Gekkio/gb-research/mbc1b/schematic/MBC1B.kicad_sch

## KiCad design mbc1b/schematic/MBC1B.kicad_sch (2024-04-07)

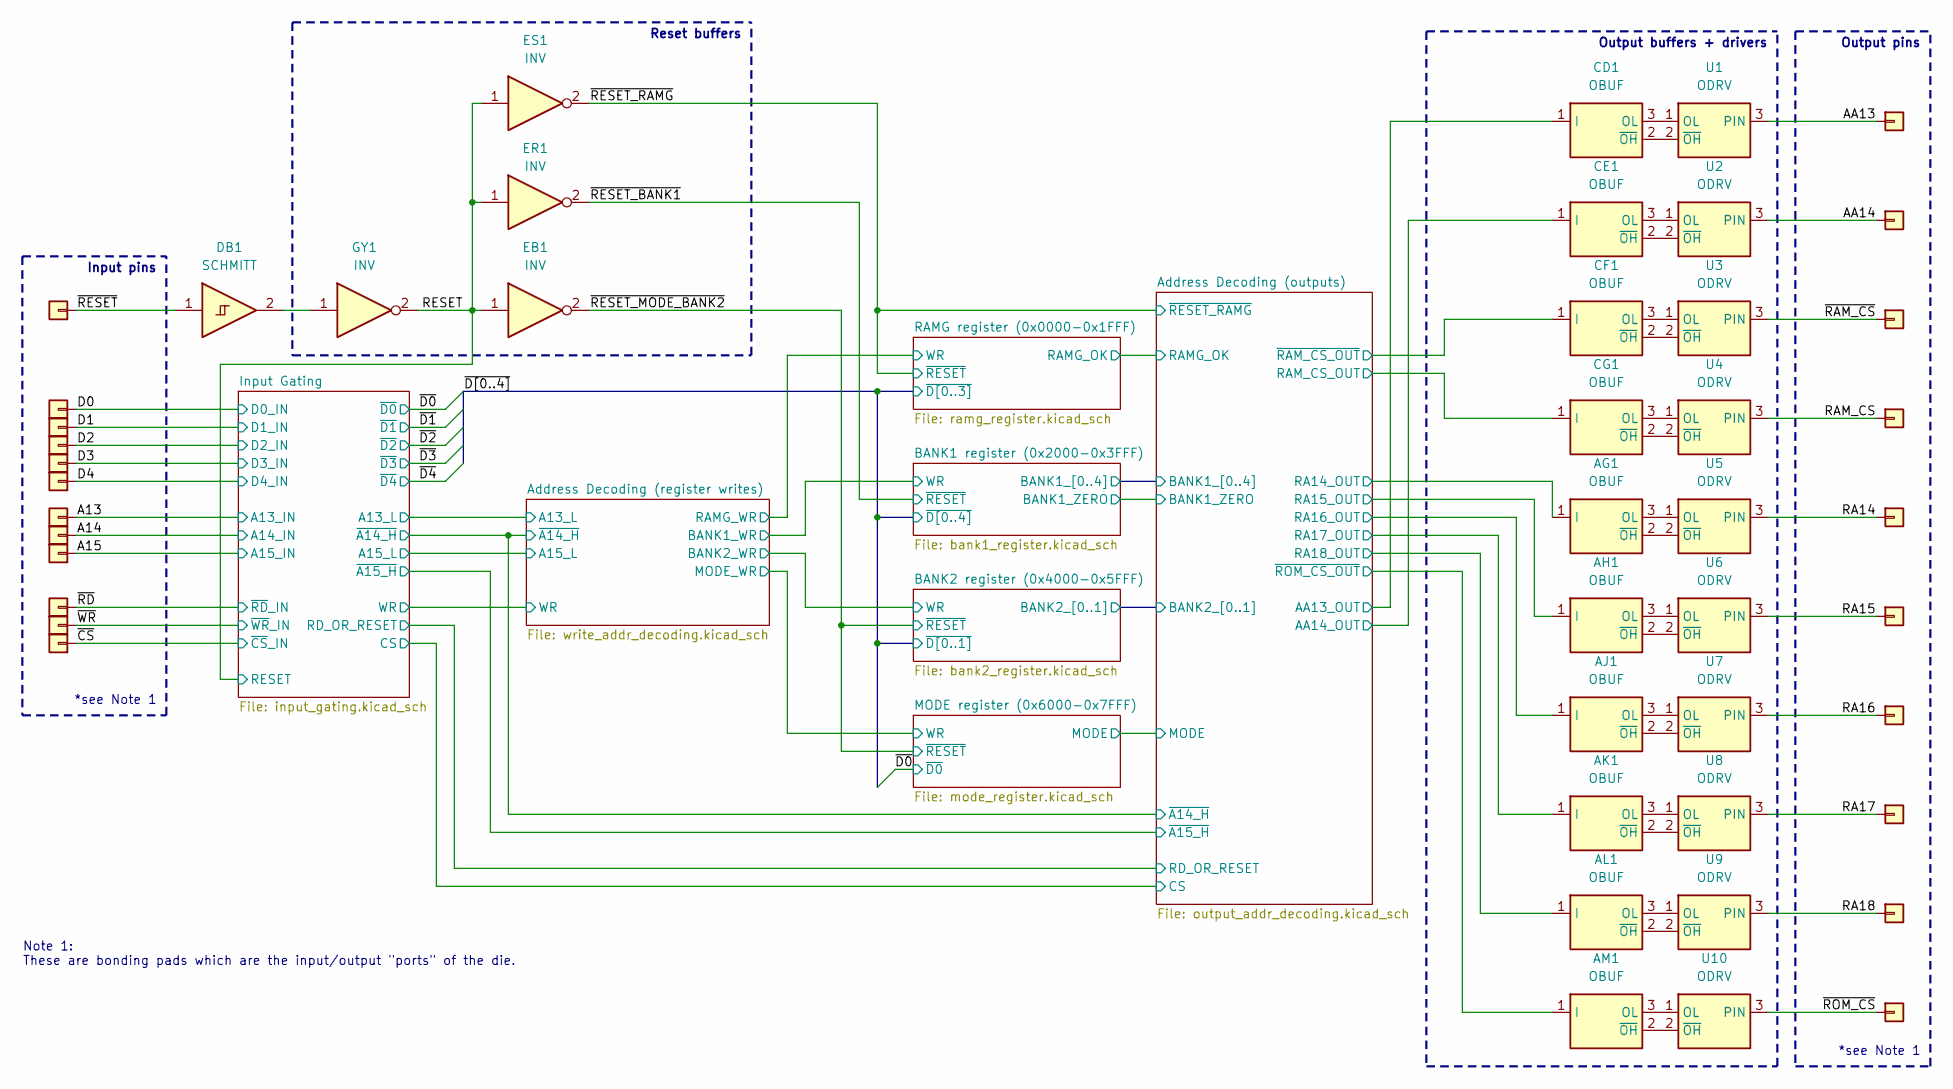
[picture p10: schematic MBC1B.kicad_sch]

Parts:
A1, A2, A3, A4, A5, A6, A7, A8, A9, A10, A11, A12, A13, A14, A15, A16, A17, A18, A19, A20, A21, A22: (no value)
AG1: OBUF
AH1: OBUF
AJ1: OBUF
AK1: OBUF
AL1: OBUF
AM1: OBUF
CD1: OBUF
CE1: OBUF
CF1: OBUF
CG1: OBUF
DB1: SCHMITT
EB1: INV
ER1: INV
ES1: INV
GY1: INV
U1, U2, U3, U4, U5, U6, U7, U8, U9, U10: ODRV

Connections:
A13: A7.1
A14: A8.1
A15: A9.1
AA13: A13.1, U1.3 (PIN)
AA13_OUT: CD1.1 (I)
AA14: A14.1, U2.3 (PIN)
AA14_OUT: CE1.1 (I)
D0: A2.1
D1: A3.1
D2: A4.1
D3: A5.1
D4: A6.1
unnamed: AG1.2 (~OH), U5.2 (~OH)
unnamed: AG1.3 (OL), U5.1 (OL)
unnamed: AH1.2 (~OH), U6.2 (~OH)
unnamed: AH1.3 (OL), U6.1 (OL)
unnamed: AJ1.2 (~OH), U7.2 (~OH)
unnamed: AJ1.3 (OL), U7.1 (OL)
unnamed: AK1.2 (~OH), U8.2 (~OH)
unnamed: AK1.3 (OL), U8.1 (OL)
unnamed: AL1.2 (~OH), U9.2 (~OH)
unnamed: AL1.3 (OL), U9.1 (OL)
unnamed: AM1.2 (~OH), U10.2 (~OH)
unnamed: AM1.3 (OL), U10.1 (OL)
unnamed: CD1.2 (~OH), U1.2 (~OH)
unnamed: CD1.3 (OL), U1.1 (OL)
unnamed: CE1.2 (~OH), U2.2 (~OH)
unnamed: CE1.3 (OL), U2.1 (OL)
unnamed: CF1.2 (~OH), U3.2 (~OH)
unnamed: CF1.3 (OL), U3.1 (OL)
unnamed: CG1.2 (~OH), U4.2 (~OH)
unnamed: CG1.3 (OL), U4.1 (OL)
unnamed: DB1.2 (Y), GY1.1 (A)
RA14: A17.1, U5.3 (PIN)
RA14_OUT: AG1.1 (I)
RA15: A18.1, U6.3 (PIN)
RA15_OUT: AH1.1 (I)
RA16: A19.1, U7.3 (PIN)
RA16_OUT: AJ1.1 (I)
RA17: A20.1, U8.3 (PIN)
RA17_OUT: AK1.1 (I)
RA18: A21.1, U9.3 (PIN)
RA18_OUT: AL1.1 (I)
RAM_CS: A16.1, U4.3 (PIN)
RAM_CS_OUT: CG1.1 (I)
RESET: EB1.1 (A), ER1.1 (A), ES1.1 (A), GY1.2 (Y)
~CS: A12.1
~RAM_CS_OUT: CF1.1 (I)
~RAM_CS: A15.1, U3.3 (PIN)
~RD: A10.1
~RESET_BANK1: ER1.2 (Y)
~RESET_MODE_BANK2: EB1.2 (Y)
~RESET_RAMG: ES1.2 (Y)
~RESET: A1.1, DB1.1 (A)
~ROM_CS_OUT: AM1.1 (I)
~ROM_CS: A22.1, U10.3 (PIN)
~WR: A11.1

Notes on the sheet:
Note 1: These are bonding pads which are the input/output "ports" of the die.
Input pins
*see Note 1
Output buffers + drivers
Output pins
Reset buffers
