Gekkio/gb-research/mbc1b/schematic/bank1_register.kicad_sch

## KiCad design mbc1b/schematic/bank1_register.kicad_sch (2024-04-07)

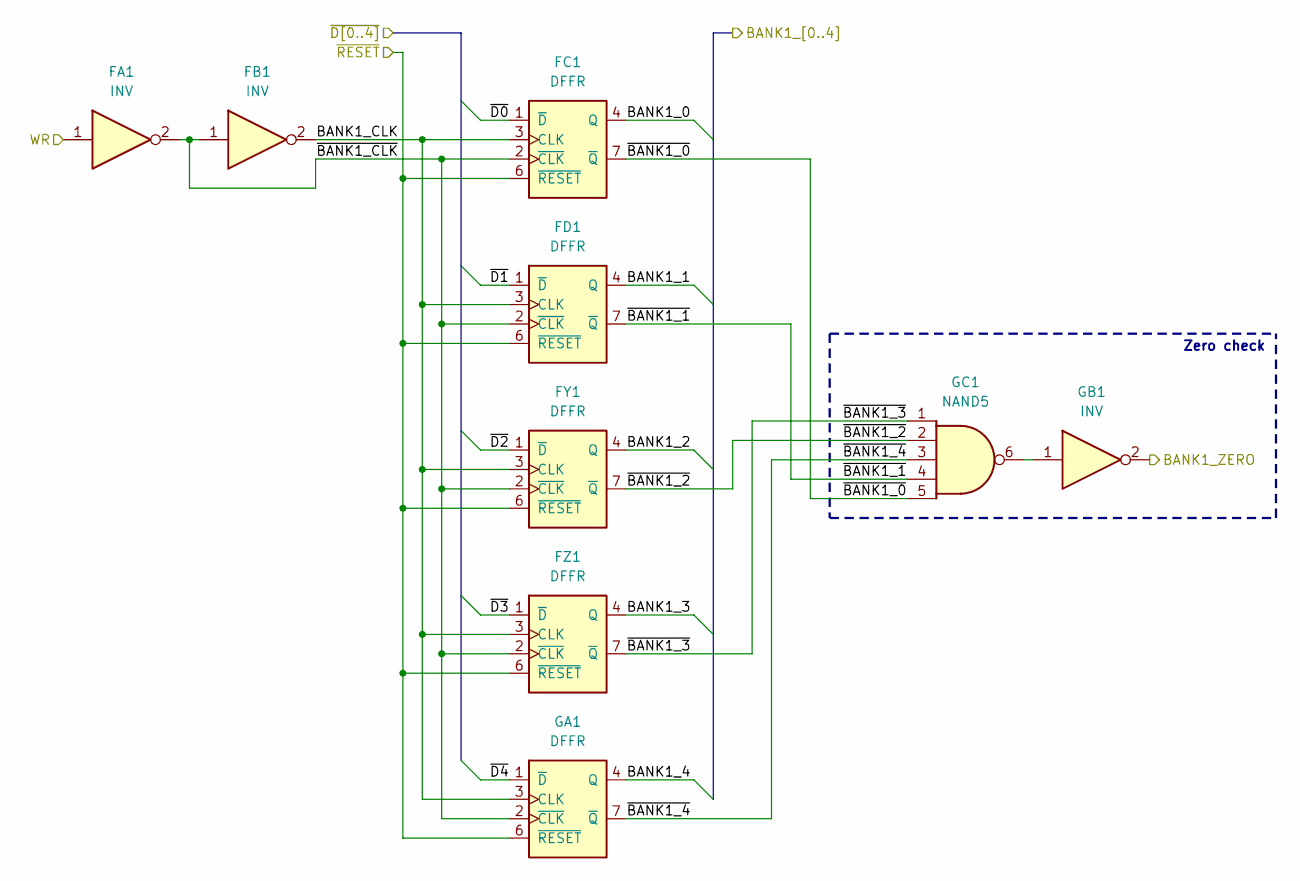
[picture p11: schematic bank1_register.kicad_sch]

Parts:
FA1: INV
FB1: INV
FC1: DFFR
FD1: DFFR
FY1: DFFR
FZ1: DFFR
GA1: DFFR
GB1: INV
GC1: NAND5

Connections:
BANK1_0: FC1.4 (Q)
BANK1_1: FD1.4 (Q)
BANK1_2: FY1.4 (Q)
BANK1_3: FZ1.4 (Q)
BANK1_4: GA1.4 (Q)
BANK1_CLK: FB1.2 (Y), FC1.3 (CLK), FD1.3 (CLK), FY1.3 (CLK), FZ1.3 (CLK), GA1.3 (CLK)
BANK1_ZERO: GB1.2 (Y)
unnamed: GB1.1 (A), GC1.6 (Y)
WR: FA1.1 (A)
~BANK1_0: FC1.7 (~Q), GC1.5 (E)
~BANK1_1: FD1.7 (~Q), GC1.4 (D)
~BANK1_2: FY1.7 (~Q), GC1.2 (B)
~BANK1_3: FZ1.7 (~Q), GC1.1 (A)
~BANK1_4: GA1.7 (~Q), GC1.3 (C)
~BANK1_CLK: FA1.2 (Y), FB1.1 (A), FC1.2 (~CLK), FD1.2 (~CLK), FY1.2 (~CLK), FZ1.2 (~CLK), GA1.2 (~CLK)
~D0: FC1.1 (~D)
~D1: FD1.1 (~D)
~D2: FY1.1 (~D)
~D3: FZ1.1 (~D)
~D4: GA1.1 (~D)
~RESET: FC1.6 (~RESET), FD1.6 (~RESET), FY1.6 (~RESET), FZ1.6 (~RESET), GA1.6 (~RESET)

Notes on the sheet:
Zero check
