Gekkio/gb-research/mbc1b/schematic/bank2_register.kicad_sch

## KiCad design mbc1b/schematic/bank2_register.kicad_sch (2024-04-07)

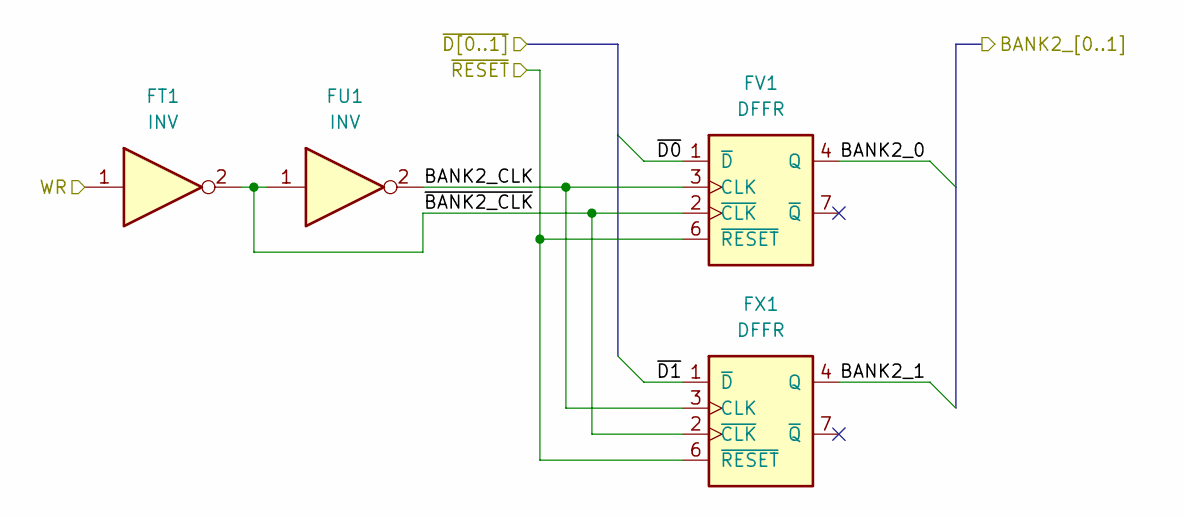
[picture p12: schematic bank2_register.kicad_sch]

Parts:
FT1: INV
FU1: INV
FV1: DFFR
FX1: DFFR

Connections:
BANK2_0: FV1.4 (Q)
BANK2_1: FX1.4 (Q)
BANK2_CLK: FU1.2 (Y), FV1.3 (CLK), FX1.3 (CLK)
WR: FT1.1 (A)
~BANK2_CLK: FT1.2 (Y), FU1.1 (A), FV1.2 (~CLK), FX1.2 (~CLK)
~D0: FV1.1 (~D)
~D1: FX1.1 (~D)
~RESET: FV1.6 (~RESET), FX1.6 (~RESET)
