Gekkio/gb-research/mbc1b/schematic/input_gates.kicad_sch

## KiCad design mbc1b/schematic/input_gates.kicad_sch (2022-03-13)

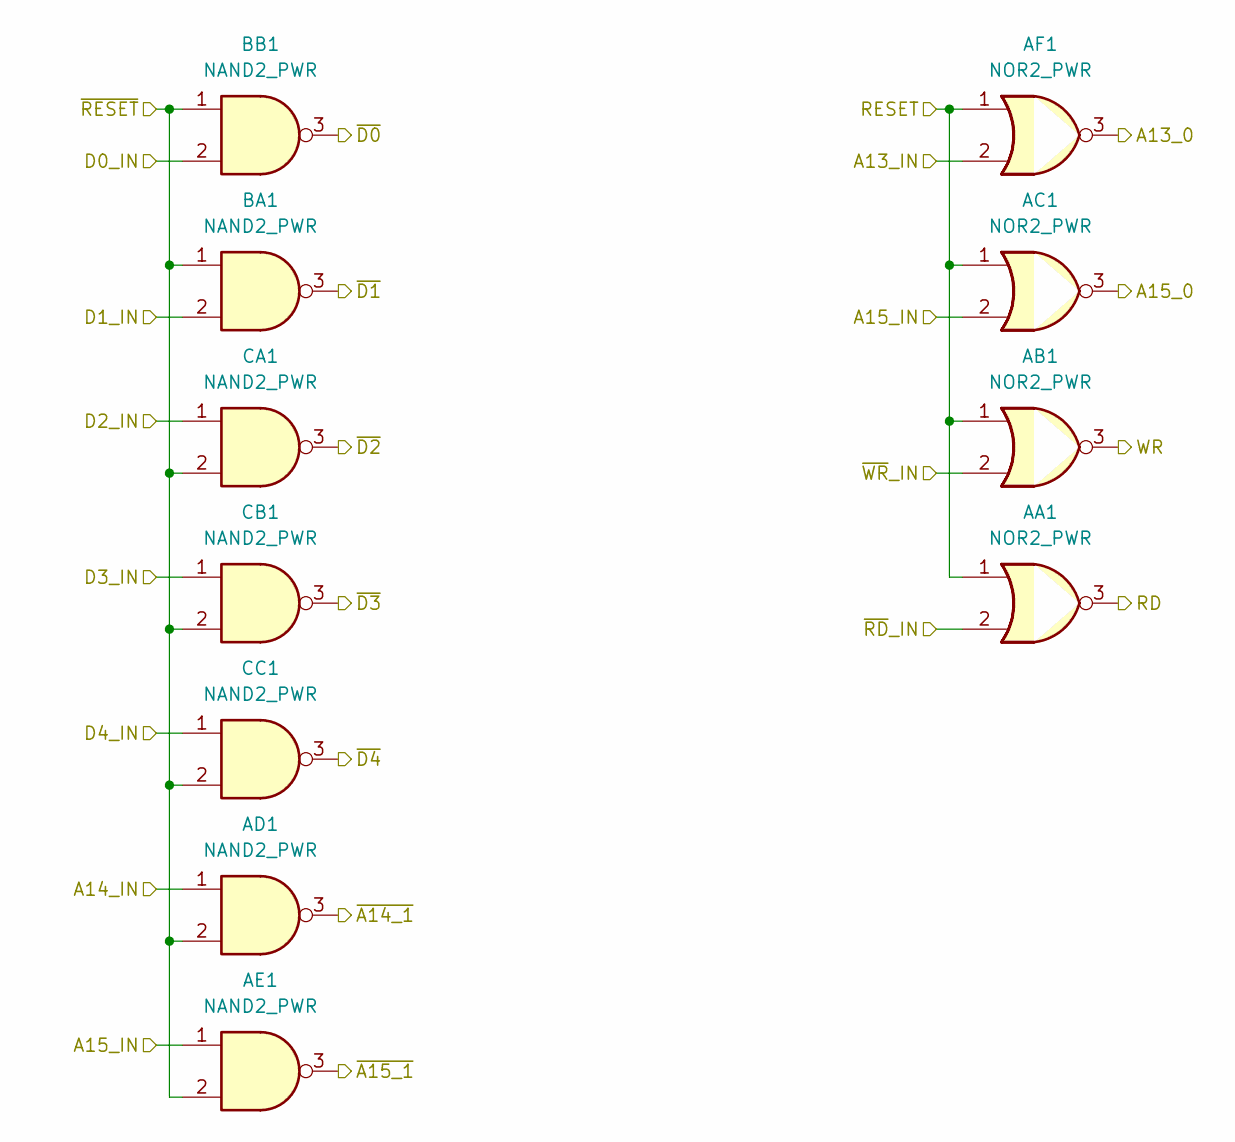
[picture p13: schematic input_gates.kicad_sch]

Parts:
AA1: NOR2_PWR
AB1: NOR2_PWR
AC1: NOR2_PWR
AD1: NAND2_PWR
AE1: NAND2_PWR
AF1: NOR2_PWR
BA1: NAND2_PWR
BB1: NAND2_PWR
CA1: NAND2_PWR
CB1: NAND2_PWR
CC1: NAND2_PWR

Connections:
A13_0: AF1.3 (Y)
A13_IN: AF1.2 (B)
A14_IN: AD1.1 (A)
A15_0: AC1.3 (Y)
A15_IN: AC1.2 (B), AE1.1 (A)
D0_IN: BB1.2 (B)
D1_IN: BA1.2 (B)
D2_IN: CA1.1 (A)
D3_IN: CB1.1 (A)
D4_IN: CC1.1 (A)
RD: AA1.3 (Y)
RESET: AA1.1 (A), AB1.1 (A), AC1.1 (A), AF1.1 (A)
WR: AB1.3 (Y)
~A14_1: AD1.3 (Y)
~A15_1: AE1.3 (Y)
~D0: BB1.3 (Y)
~D1: BA1.3 (Y)
~D2: CA1.3 (Y)
~D3: CB1.3 (Y)
~D4: CC1.3 (Y)
~RD_IN: AA1.2 (B)
~RESET: AD1.2 (B), AE1.2 (B), BA1.1 (A), BB1.1 (A), CA1.2 (B), CB1.2 (B), CC1.2 (B)
~WR_IN: AB1.2 (B)
