Gekkio/gb-research/mbc1b/schematic/input_gating.kicad_sch

## KiCad design mbc1b/schematic/input_gating.kicad_sch (2024-04-07)

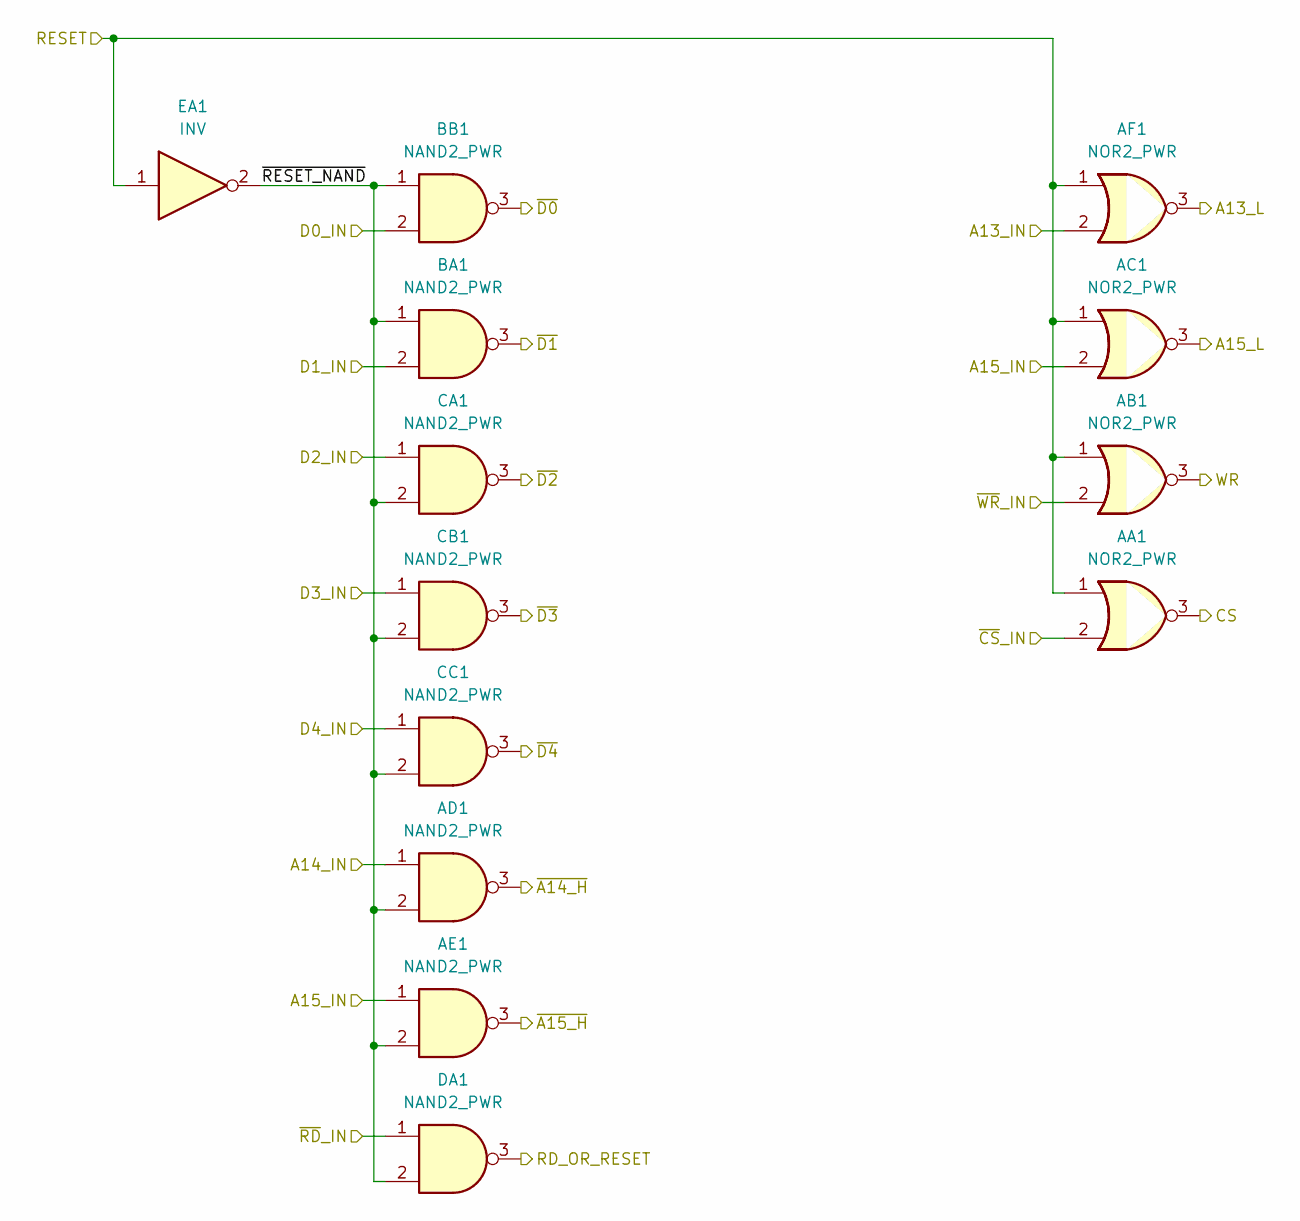
[picture p14: schematic input_gating.kicad_sch]

Parts:
AA1: NOR2_PWR
AB1: NOR2_PWR
AC1: NOR2_PWR
AD1: NAND2_PWR
AE1: NAND2_PWR
AF1: NOR2_PWR
BA1: NAND2_PWR
BB1: NAND2_PWR
CA1: NAND2_PWR
CB1: NAND2_PWR
CC1: NAND2_PWR
DA1: NAND2_PWR
EA1: INV

Connections:
A13_IN: AF1.2 (B)
A13_L: AF1.3 (Y)
A14_IN: AD1.1 (A)
A15_IN: AC1.2 (B), AE1.1 (A)
A15_L: AC1.3 (Y)
CS: AA1.3 (Y)
D0_IN: BB1.2 (B)
D1_IN: BA1.2 (B)
D2_IN: CA1.1 (A)
D3_IN: CB1.1 (A)
D4_IN: CC1.1 (A)
RD_OR_RESET: DA1.3 (Y)
RESET: AA1.1 (A), AB1.1 (A), AC1.1 (A), AF1.1 (A), EA1.1 (A)
WR: AB1.3 (Y)
~A14_H: AD1.3 (Y)
~A15_H: AE1.3 (Y)
~CS_IN: AA1.2 (B)
~D0: BB1.3 (Y)
~D1: BA1.3 (Y)
~D2: CA1.3 (Y)
~D3: CB1.3 (Y)
~D4: CC1.3 (Y)
~RD_IN: DA1.1 (A)
~RESET_NAND: AD1.2 (B), AE1.2 (B), BA1.1 (A), BB1.1 (A), CA1.2 (B), CB1.2 (B), CC1.2 (B), DA1.2 (B), EA1.2 (Y)
~WR_IN: AB1.2 (B)
