Gekkio/gb-research/mbc1b/schematic/mode_register.kicad_sch

## KiCad design mbc1b/schematic/mode_register.kicad_sch (2024-04-07)

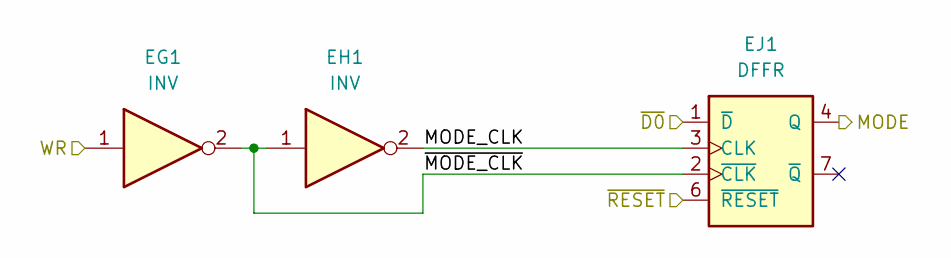
[picture p15: schematic mode_register.kicad_sch]

Parts:
EG1: INV
EH1: INV
EJ1: DFFR

Connections:
MODE: EJ1.4 (Q)
MODE_CLK: EH1.2 (Y), EJ1.3 (CLK)
WR: EG1.1 (A)
~D0: EJ1.1 (~D)
~MODE_CLK: EG1.2 (Y), EH1.1 (A), EJ1.2 (~CLK)
~RESET: EJ1.6 (~RESET)
