Gekkio/gb-research/mbc1b/schematic/output_addr_decoding.kicad_sch

## KiCad design mbc1b/schematic/output_addr_decoding.kicad_sch (2024-04-07)

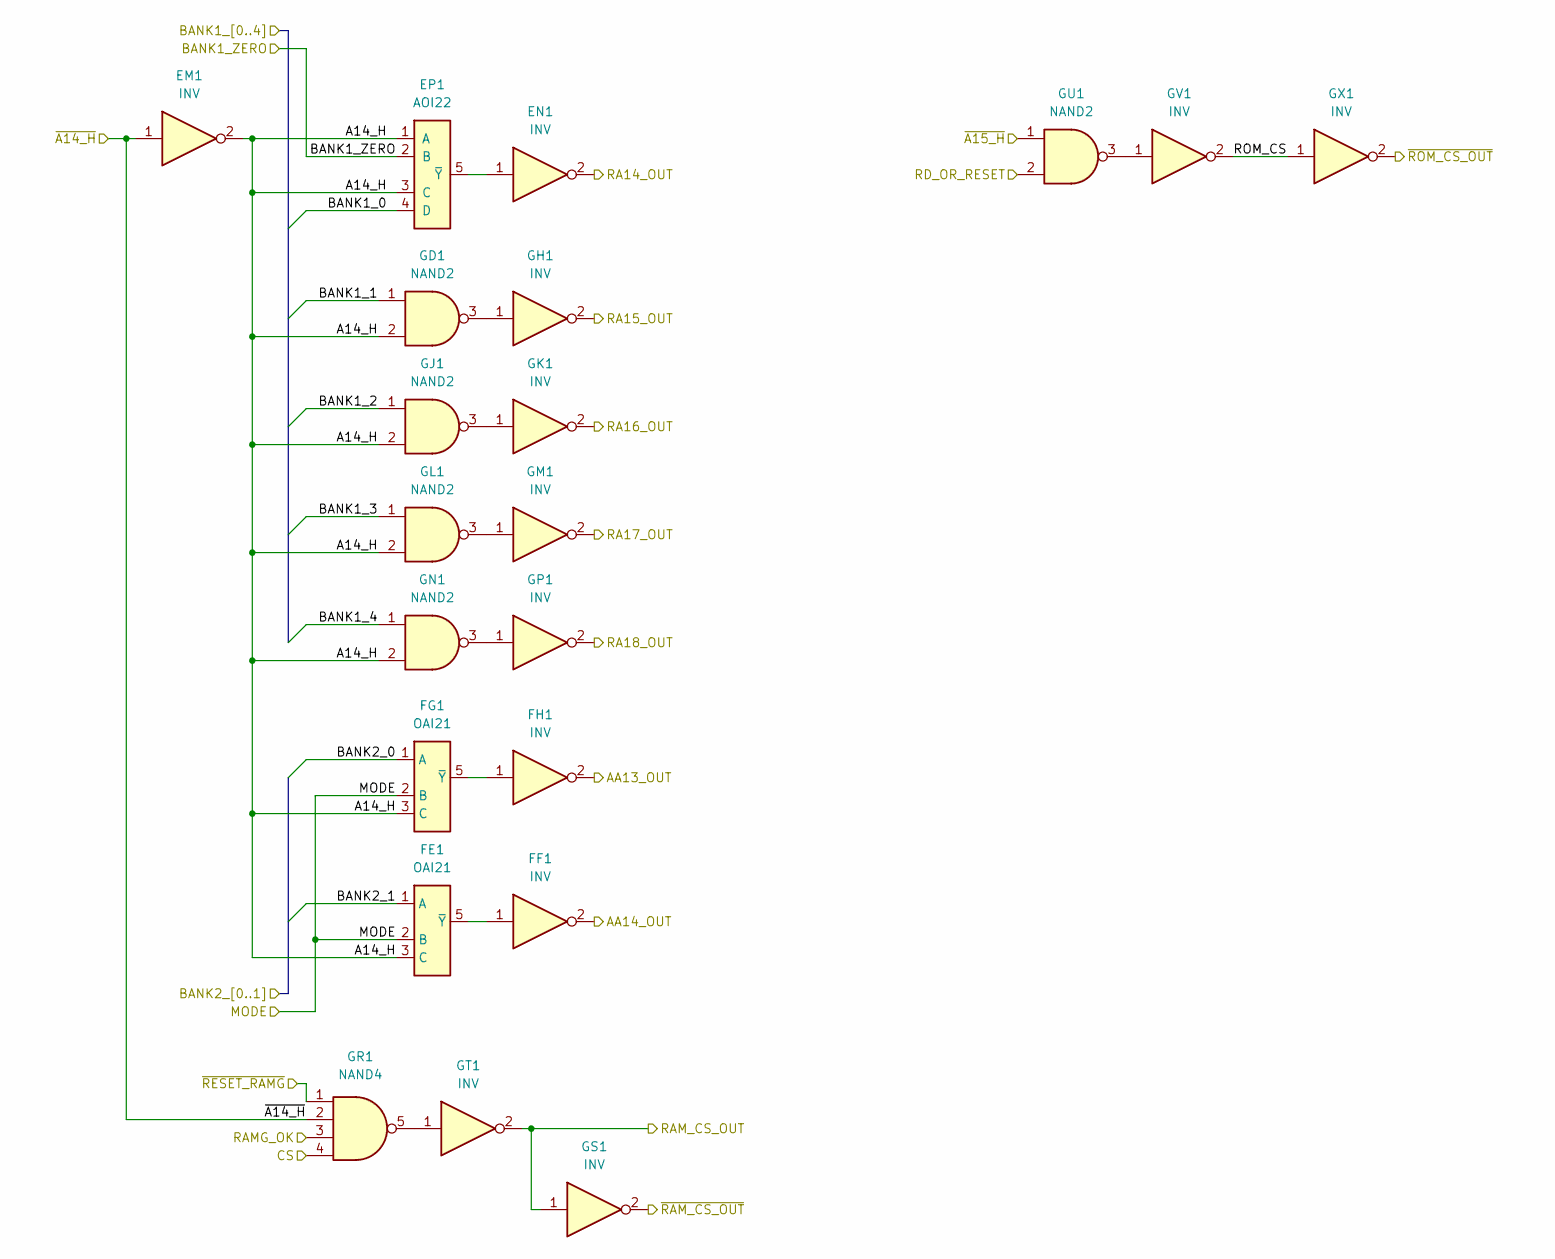
[picture p16: schematic output_addr_decoding.kicad_sch]

Parts:
EM1: INV
EN1: INV
EP1: AOI22
FE1: OAI21
FF1: INV
FG1: OAI21
FH1: INV
GD1: NAND2
GH1: INV
GJ1: NAND2
GK1: INV
GL1: NAND2
GM1: INV
GN1: NAND2
GP1: INV
GR1: NAND4
GS1: INV
GT1: INV
GU1: NAND2
GV1: INV
GX1: INV

Connections:
A14_H: EM1.2 (Y), EP1.1 (A), EP1.3 (C), FE1.3 (C), FG1.3 (C), GD1.2 (B), GJ1.2 (B), GL1.2 (B), GN1.2 (B)
AA13_OUT: FH1.2 (Y)
AA14_OUT: FF1.2 (Y)
BANK1_0: EP1.4 (D)
BANK1_1: GD1.1 (A)
BANK1_2: GJ1.1 (A)
BANK1_3: GL1.1 (A)
BANK1_4: GN1.1 (A)
BANK1_ZERO: EP1.2 (B)
BANK2_0: FG1.1 (A)
BANK2_1: FE1.1 (A)
CS: GR1.4 (D)
MODE: FE1.2 (B), FG1.2 (B)
unnamed: EN1.1 (A), EP1.5 (~Y)
unnamed: FE1.5 (~Y), FF1.1 (A)
unnamed: FG1.5 (~Y), FH1.1 (A)
unnamed: GD1.3 (Y), GH1.1 (A)
unnamed: GJ1.3 (Y), GK1.1 (A)
unnamed: GL1.3 (Y), GM1.1 (A)
unnamed: GN1.3 (Y), GP1.1 (A)
unnamed: GR1.5 (Y), GT1.1 (A)
unnamed: GU1.3 (Y), GV1.1 (A)
RA14_OUT: EN1.2 (Y)
RA15_OUT: GH1.2 (Y)
RA16_OUT: GK1.2 (Y)
RA17_OUT: GM1.2 (Y)
RA18_OUT: GP1.2 (Y)
RAMG_OK: GR1.3 (C)
RAM_CS_OUT: GS1.1 (A), GT1.2 (Y)
RD_OR_RESET: GU1.2 (B)
ROM_CS: GV1.2 (Y), GX1.1 (A)
~A14_H: EM1.1 (A), GR1.2 (B)
~A15_H: GU1.1 (A)
~RAM_CS_OUT: GS1.2 (Y)
~RESET_RAMG: GR1.1 (A)
~ROM_CS_OUT: GX1.2 (Y)
