Gekkio/gb-research/mbc1b/schematic/output_drivers.kicad_sch

## KiCad design mbc1b/schematic/output_drivers.kicad_sch (2022-03-13)

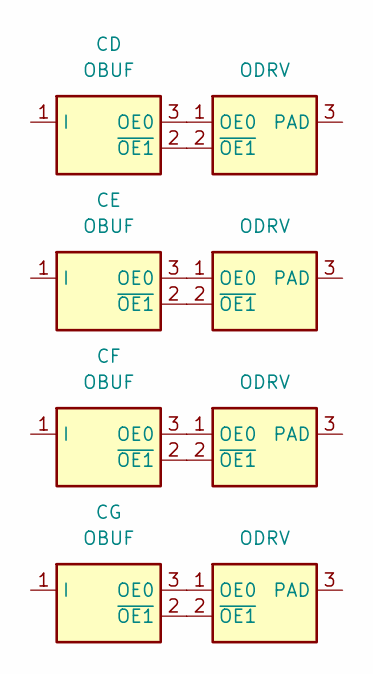
[picture p17: schematic output_drivers.kicad_sch]

Parts:
CD: OBUF
CE: OBUF
CF: OBUF
CG: OBUF
