Gekkio/gb-research/mbc1b/schematic/ramg_register.kicad_sch

## KiCad design mbc1b/schematic/ramg_register.kicad_sch (2024-04-07)

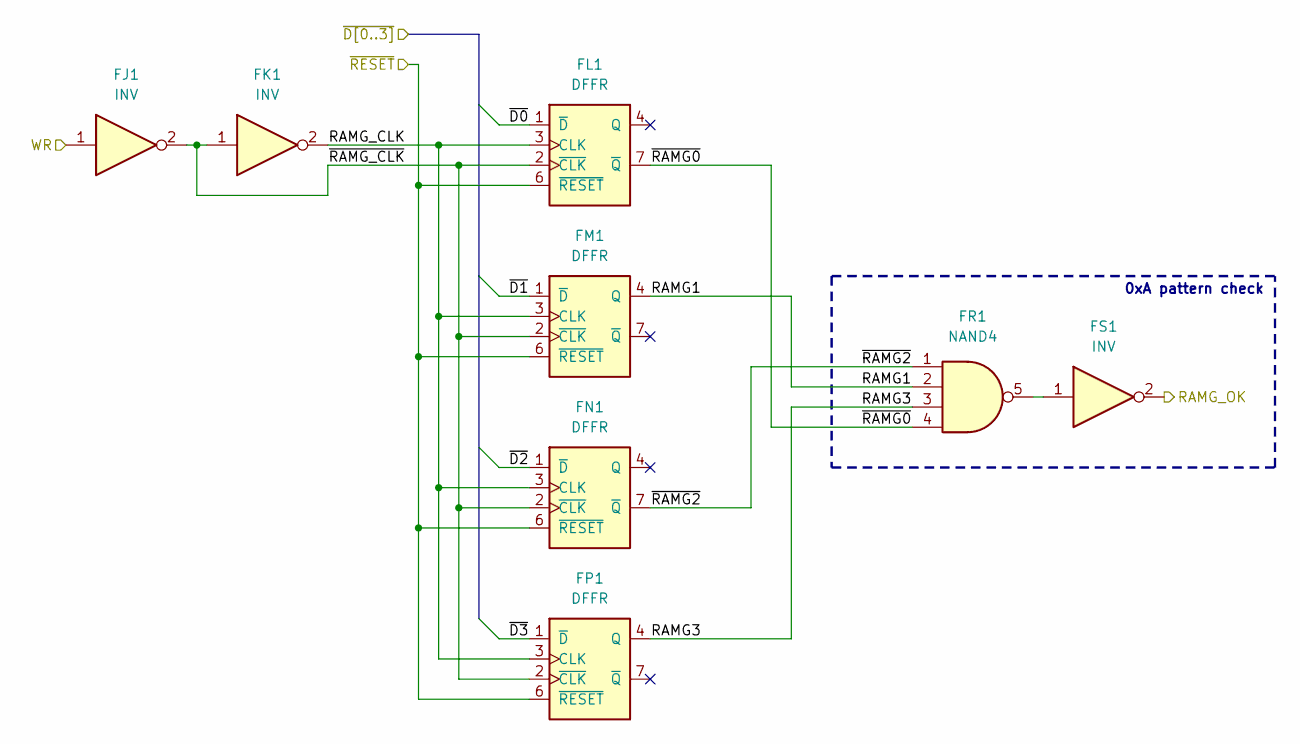
[picture p18: schematic ramg_register.kicad_sch]

Parts:
FJ1: INV
FK1: INV
FL1: DFFR
FM1: DFFR
FN1: DFFR
FP1: DFFR
FR1: NAND4
FS1: INV

Connections:
unnamed: FR1.5 (Y), FS1.1 (A)
RAMG1: FM1.4 (Q), FR1.2 (B)
RAMG3: FP1.4 (Q), FR1.3 (C)
RAMG_CLK: FK1.2 (Y), FL1.3 (CLK), FM1.3 (CLK), FN1.3 (CLK), FP1.3 (CLK)
RAMG_OK: FS1.2 (Y)
WR: FJ1.1 (A)
~D0: FL1.1 (~D)
~D1: FM1.1 (~D)
~D2: FN1.1 (~D)
~D3: FP1.1 (~D)
~RAMG0: FL1.7 (~Q), FR1.4 (D)
~RAMG2: FN1.7 (~Q), FR1.1 (A)
~RAMG_CLK: FJ1.2 (Y), FK1.1 (A), FL1.2 (~CLK), FM1.2 (~CLK), FN1.2 (~CLK), FP1.2 (~CLK)
~RESET: FL1.6 (~RESET), FM1.6 (~RESET), FN1.6 (~RESET), FP1.6 (~RESET)

Notes on the sheet:
0xA pattern check
