Gekkio/gb-research/mbc1b/schematic/write_addr_decoding.kicad_sch

## KiCad design mbc1b/schematic/write_addr_decoding.kicad_sch (2024-04-07)

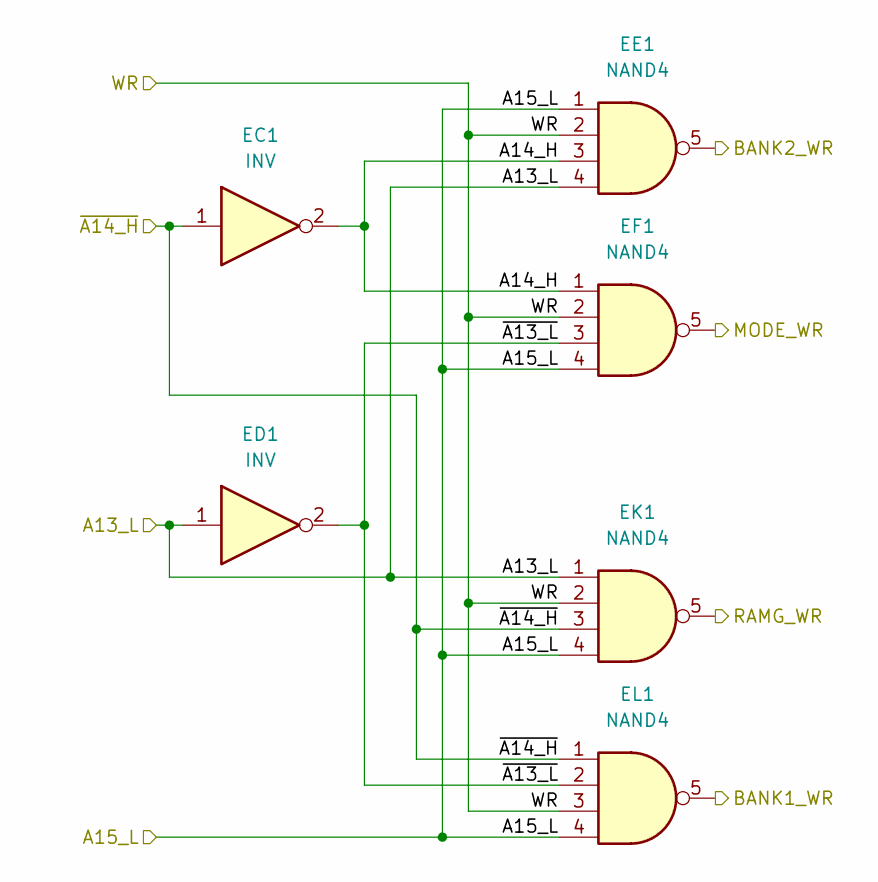
[picture p19: schematic write_addr_decoding.kicad_sch]

Parts:
EC1: INV
ED1: INV
EE1: NAND4
EF1: NAND4
EK1: NAND4
EL1: NAND4

Connections:
A13_L: ED1.1 (A), EE1.4 (D), EK1.1 (A)
A14_H: EC1.2 (Y), EE1.3 (C), EF1.1 (A)
A15_L: EE1.1 (A), EF1.4 (D), EK1.4 (D), EL1.4 (D)
BANK1_WR: EL1.5 (Y)
BANK2_WR: EE1.5 (Y)
MODE_WR: EF1.5 (Y)
RAMG_WR: EK1.5 (Y)
WR: EE1.2 (B), EF1.2 (B), EK1.2 (B), EL1.3 (C)
~A13_L: ED1.2 (Y), EF1.3 (C), EL1.2 (B)
~A14_H: EC1.1 (A), EK1.3 (C), EL1.1 (A)
